whowechina/chord_pico/ref/GJqL9p1aUAAI2bQ.jpg

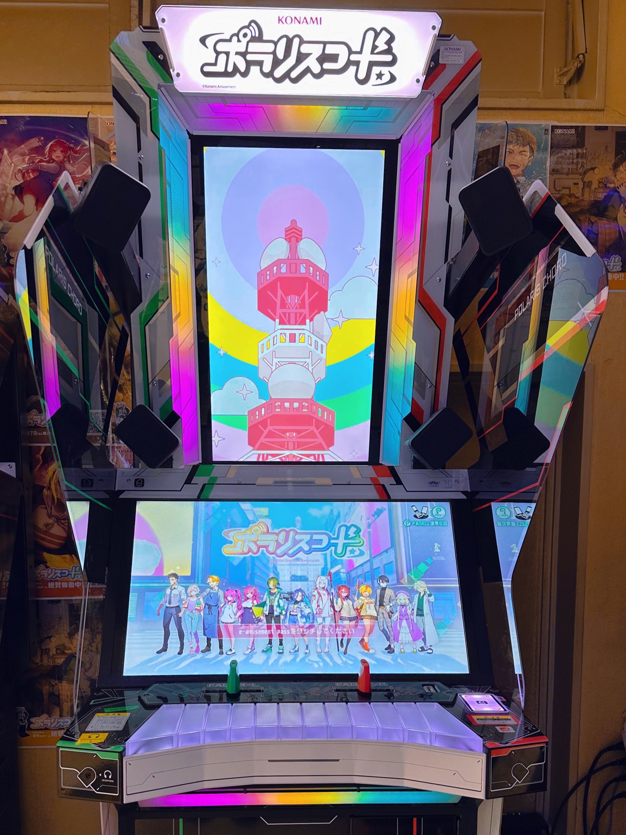
ref/GJqL9p1aUAAI2bQ.jpg
