whowechina/chord_pico/ref/Knob.png

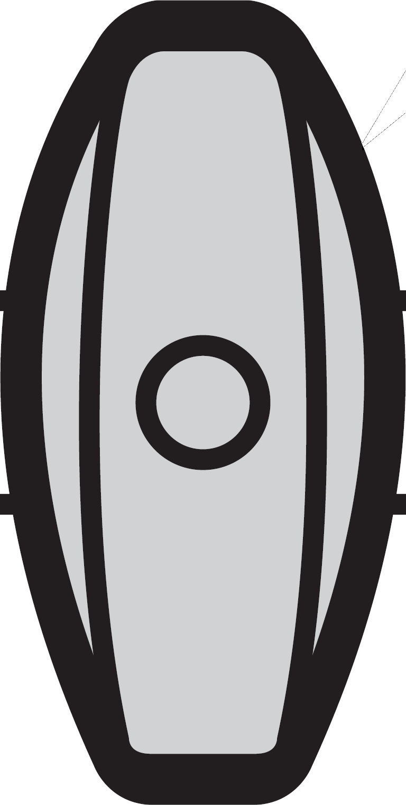
ref/Knob.png
