whowechina/chord_pico/ref/Panel2.png

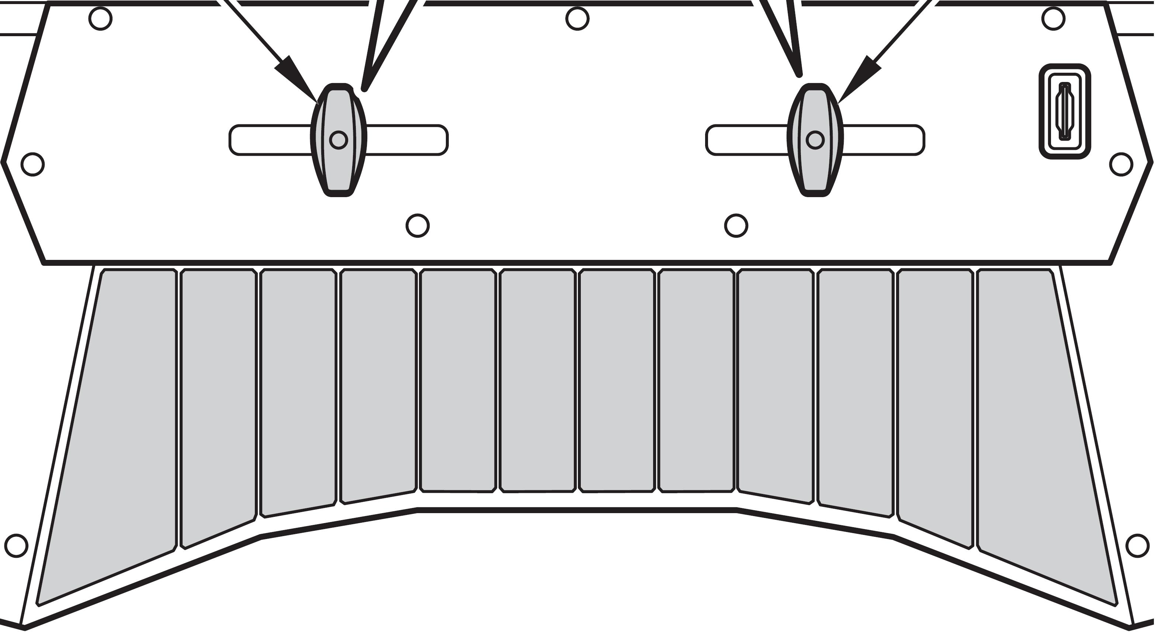
ref/Panel2.png
