whowechina/chord_pico/ref/Panel.png

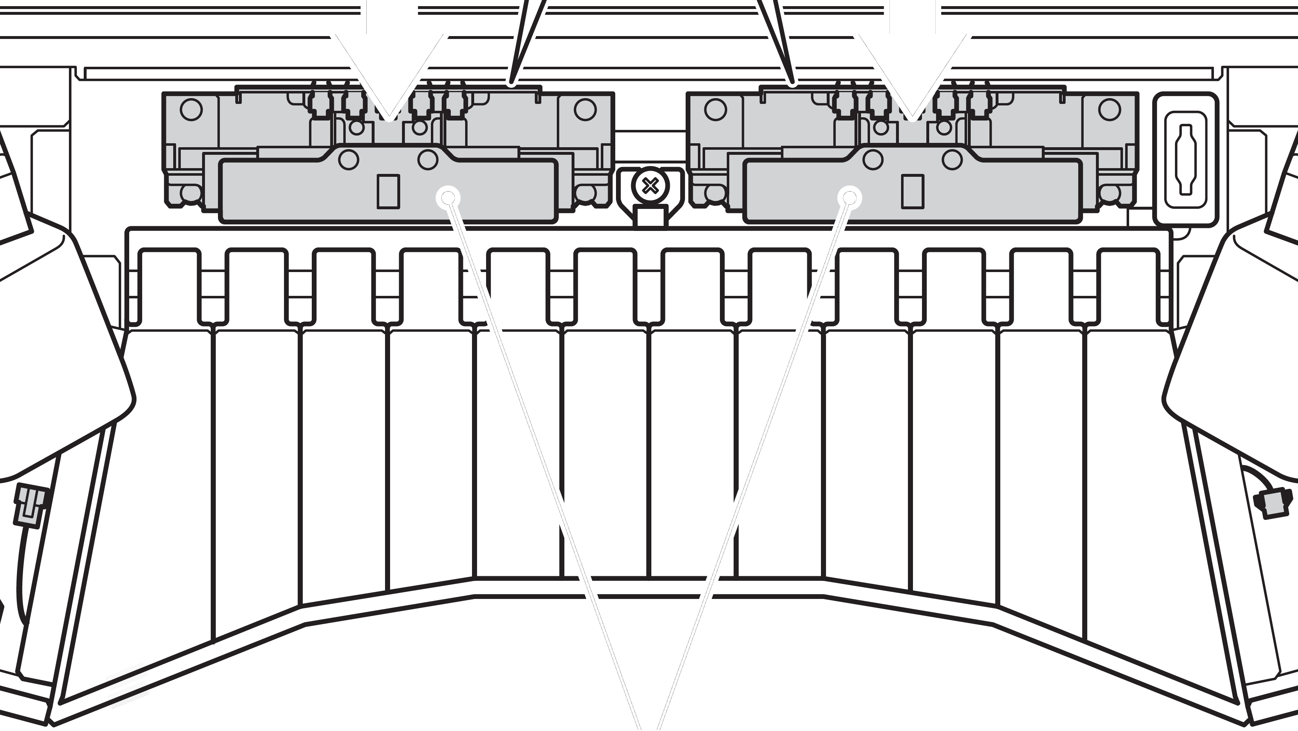
ref/Panel.png
