whowechina/chord_pico/Production/3DPrint/Chord Pico+ - BrimLeft.stl

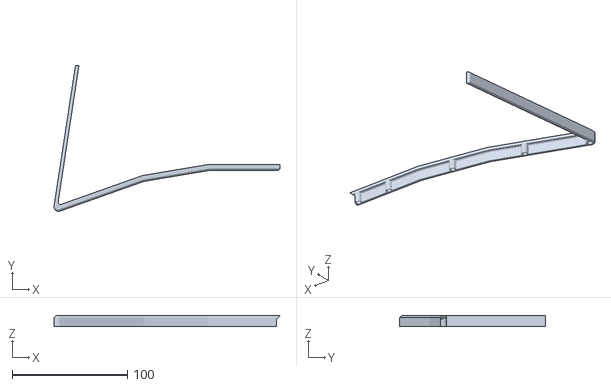
[picture p42: CAD file, 2026-01-07]
Production/3DPrint/Chord Pico+ - BrimLeft.stl
196.0 x 126.4 x 9.20
