whowechina/chord_pico/PCB/plus/3dmodels/TRS Jack PJ-313.stp

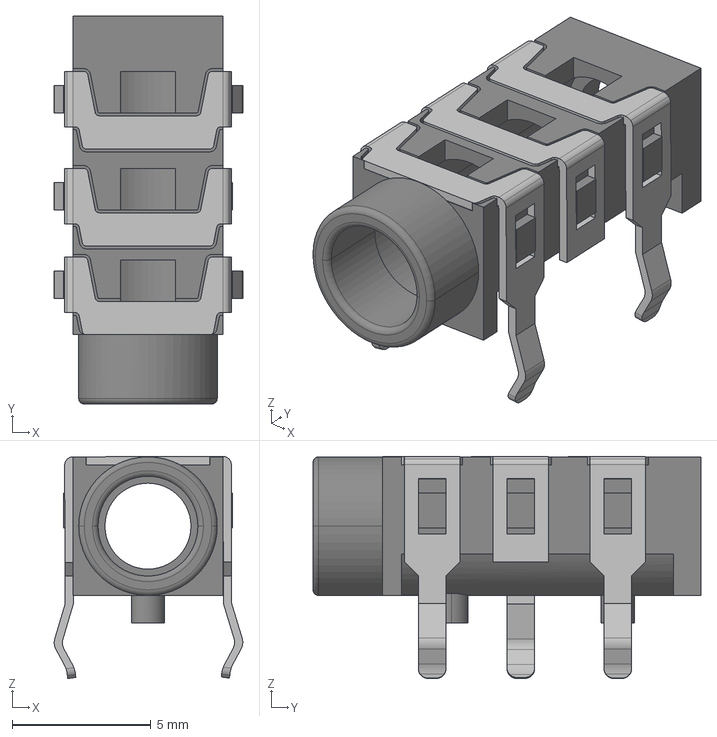
[picture p43: CAD file, 2025-06-20]
PCB/plus/3dmodels/TRS Jack PJ-313.stp
6.81 x 14.0 x 8.02 mm
