whowechina/chord_pico/Production/3DPrint/Chord Pico+ - BrimRight.stl

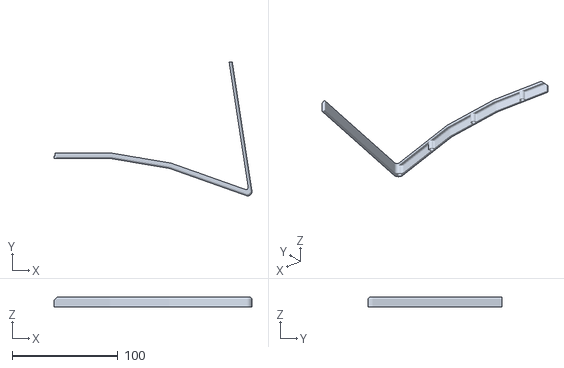
[picture p44: CAD file, 2026-01-07]
Production/3DPrint/Chord Pico+ - BrimRight.stl
187.0 x 126.4 x 9.20
