whowechina/chord_pico/PCB/plus/3dmodels/SW_Kailh_Choc_V1.stp

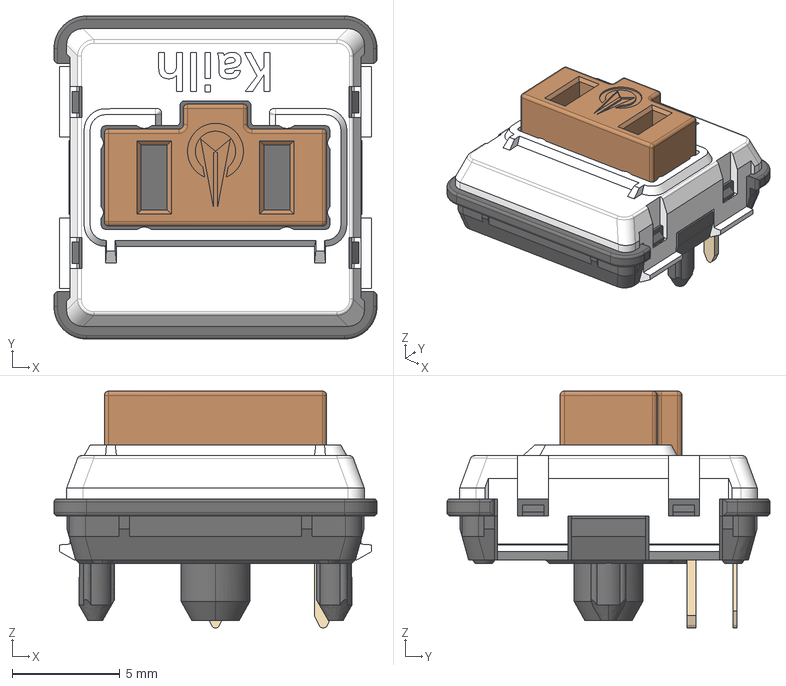
[picture p45: CAD file, 2025-06-20]
PCB/plus/3dmodels/SW_Kailh_Choc_V1.stp
15.0 x 15.0 x 11.0 mm
