whowechina/chord_pico/Production/3DPrint/Fader+ - Reflector.stl

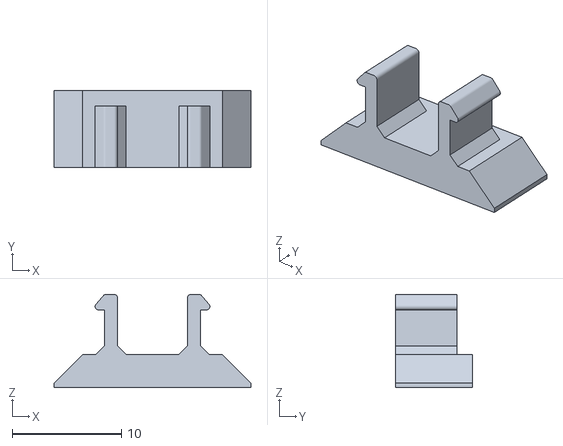
[picture p46: CAD file, 2026-01-07]
Production/3DPrint/Fader+ - Reflector.stl
18.0 x 7.00 x 8.50
