whowechina/chord_pico/Production/3DPrint/Chord Pico+ - Right.stl

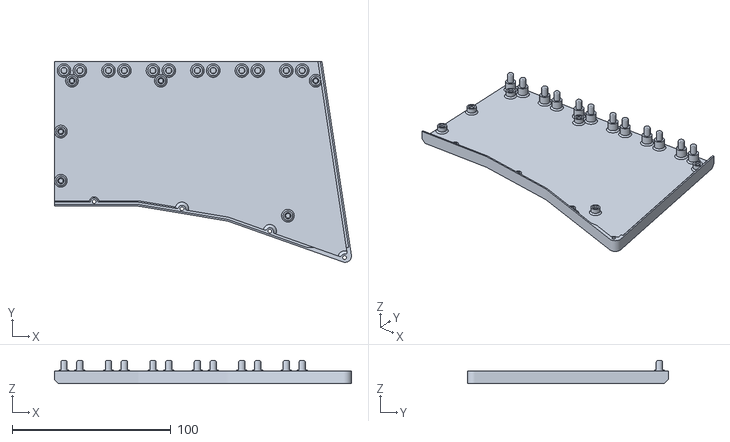
[picture p48: CAD file, 2026-01-07]
Production/3DPrint/Chord Pico+ - Right.stl
187.0 x 126.4 x 14.5
