whowechina/chord_pico/PCB/plus/3dmodels/SPEAKER_SMD_1340.STEP

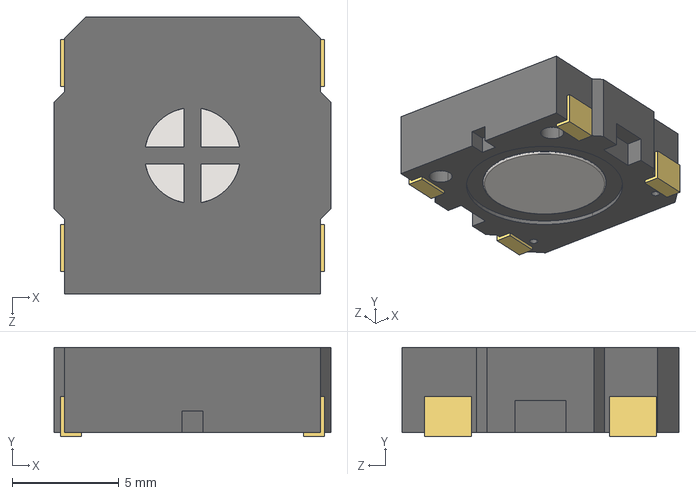
[picture p49: CAD file, 2025-06-20]
PCB/plus/3dmodels/SPEAKER_SMD_1340.STEP
13.0 x 4.20 x 13.0 mm
