whowechina/chord_pico/Production/3DPrint/Fader+ - Seat+.stl

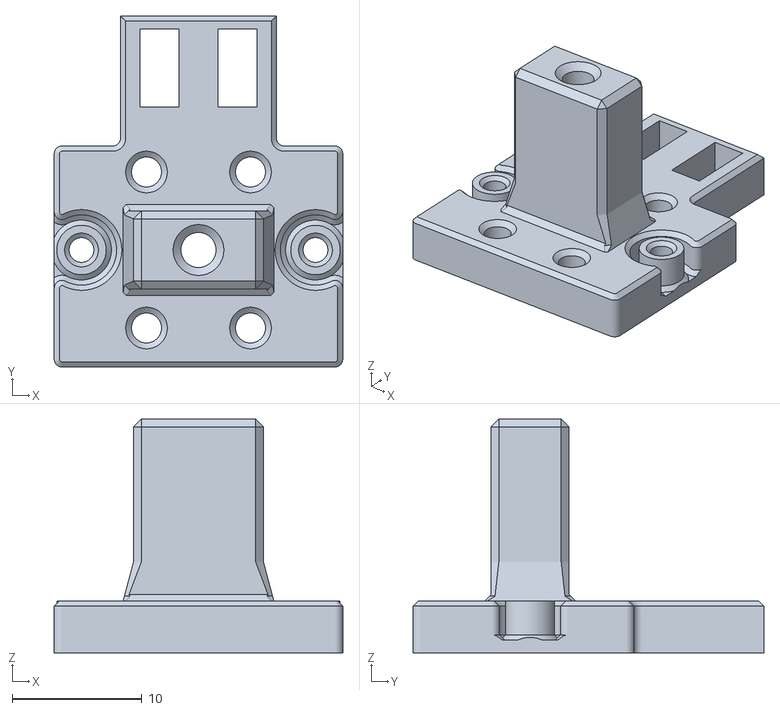
[picture p50: CAD file, 2026-01-07]
Production/3DPrint/Fader+ - Seat+.stl
22.2 x 27.0 x 18.0
