whowechina/chord_pico/PCB/plus/3dmodels/8002A.step

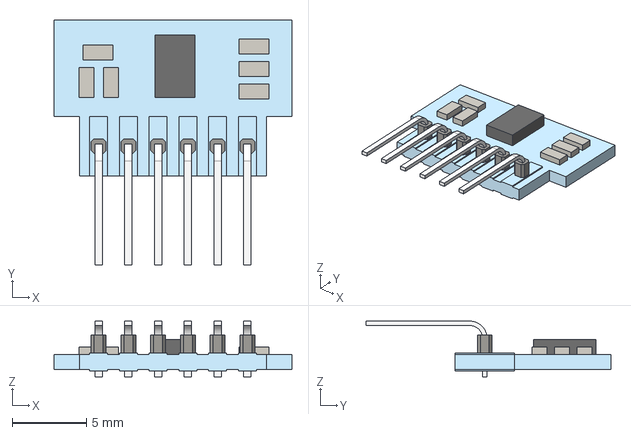
[picture p51: CAD file, 2025-06-20]
PCB/plus/3dmodels/8002A.step
16.0 x 16.5 x 3.75 mm
