whowechina/chord_pico/Production/3DPrint/Chord Pico+ - Left.stl

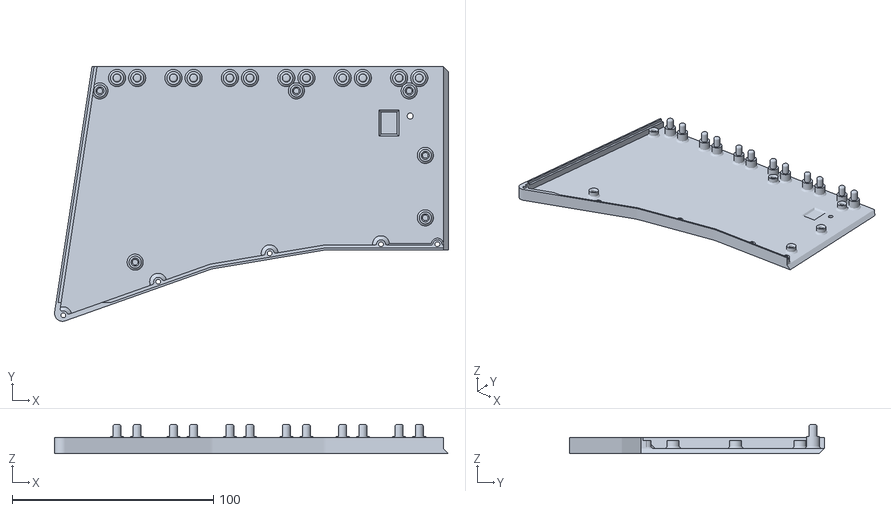
[picture p52: CAD file, 2026-01-07]
Production/3DPrint/Chord Pico+ - Left.stl
195.5 x 126.4 x 14.5
