whowechina/chord_pico/PCB/plus/3dmodels/WS2812B.step

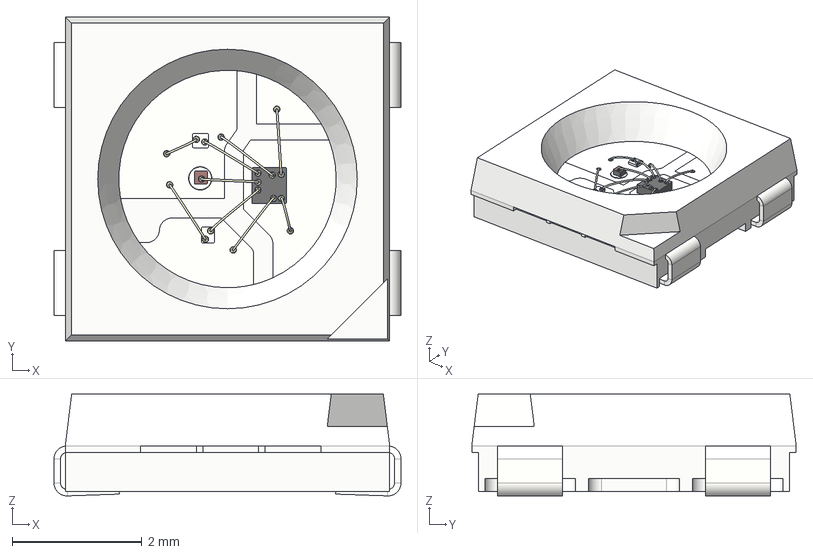
[picture p53: CAD file, 2025-06-20]
PCB/plus/3dmodels/WS2812B.step
5.35 x 5.00 x 1.57 mm
