whowechina/chord_pico/Production/3DPrint/Chord Pico+ - Rear.stl

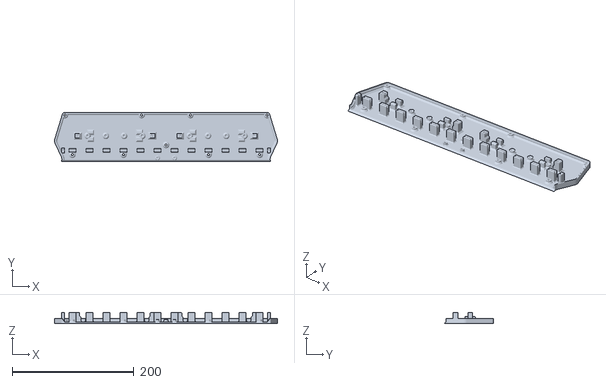
[picture p54: CAD file, 2026-01-07]
Production/3DPrint/Chord Pico+ - Rear.stl
366.7 x 81.1 x 18.2
