whowechina/chord_pico/Production/3DPrint/Fader - Slider PTFE.stl

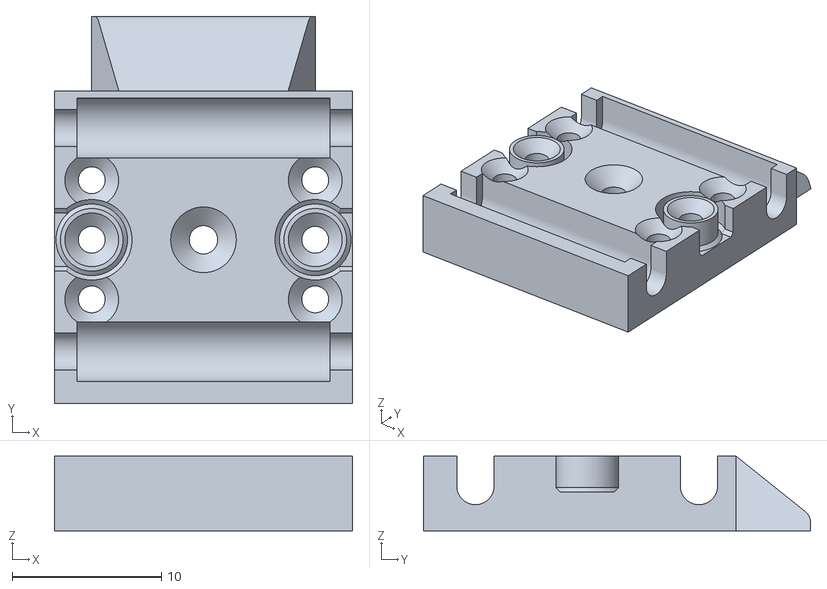
[picture p56: CAD file, 2025-09-20]
Production/3DPrint/Fader - Slider PTFE.stl
20.0 x 26.0 x 5.00
