whowechina/chord_pico/PCB/plus/3dmodels/skhhana010.stp

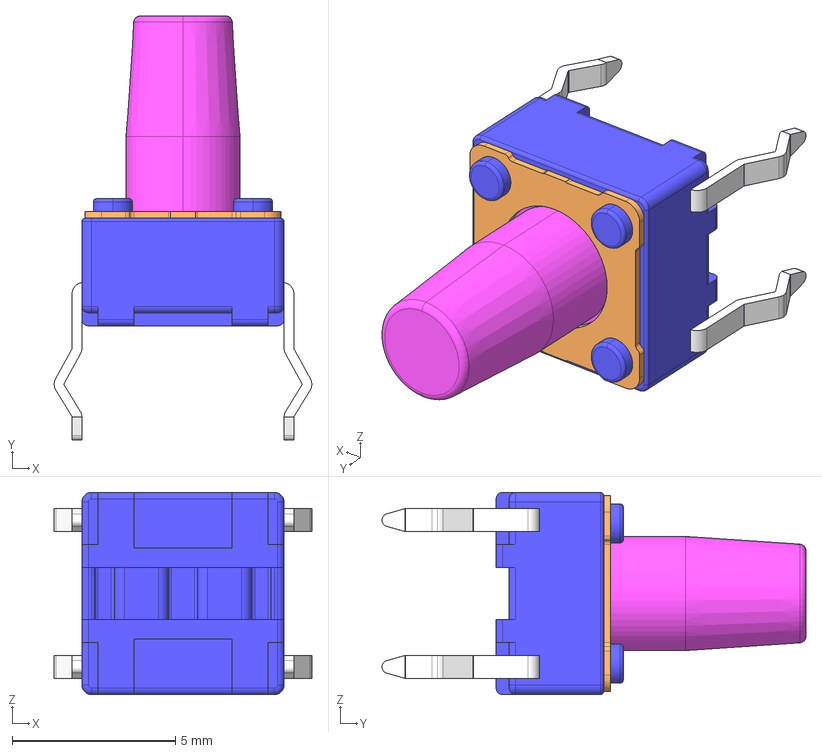
[picture p57: CAD file, 2025-06-20]
PCB/plus/3dmodels/skhhana010.stp
7.90 x 13.0 x 6.20 mm
