whowechina/chord_pico/Production/3DPrint/Fader - Slider Thruhole.stl

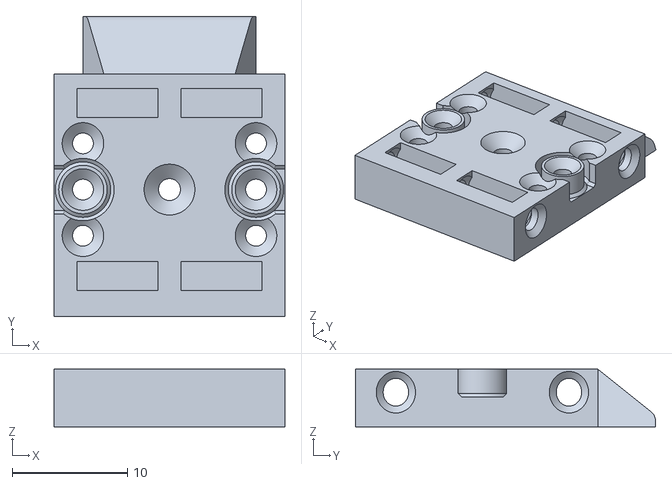
[picture p58: CAD file, 2025-09-20]
Production/3DPrint/Fader - Slider Thruhole.stl
20.0 x 26.0 x 5.00
