whowechina/chord_pico/PCB/plus/3dmodels/SKRRABE010.stp

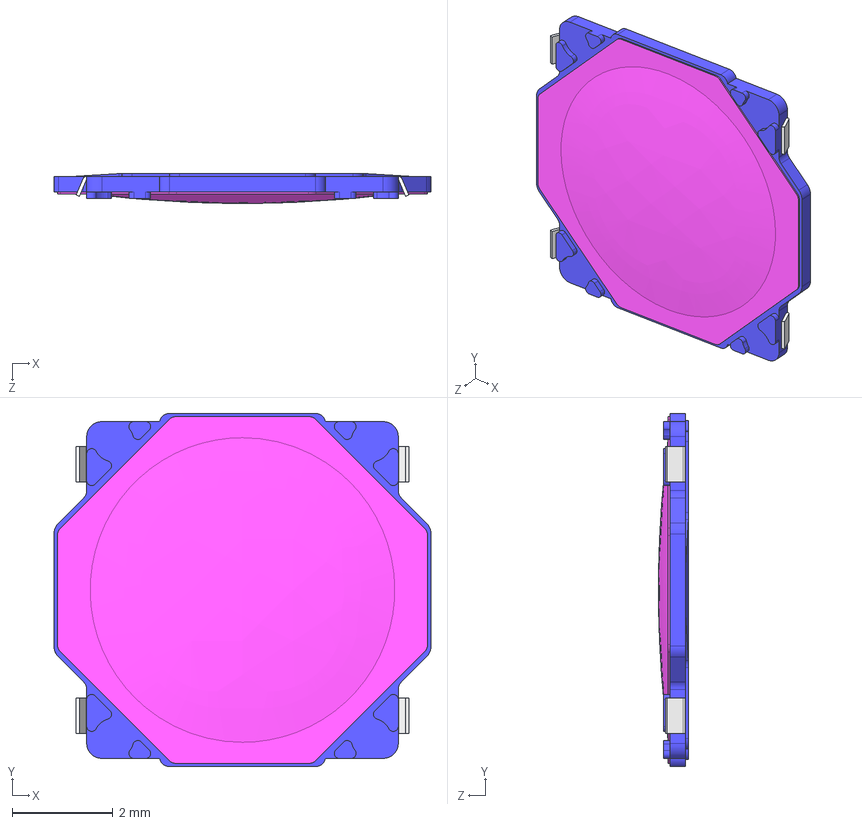
[picture p59: CAD file, 2025-06-20]
PCB/plus/3dmodels/SKRRABE010.stp
7.50 x 7.03 x 0.6 mm
