whowechina/chord_pico/Production/3DPrint/Fader - Slider Seal.stl

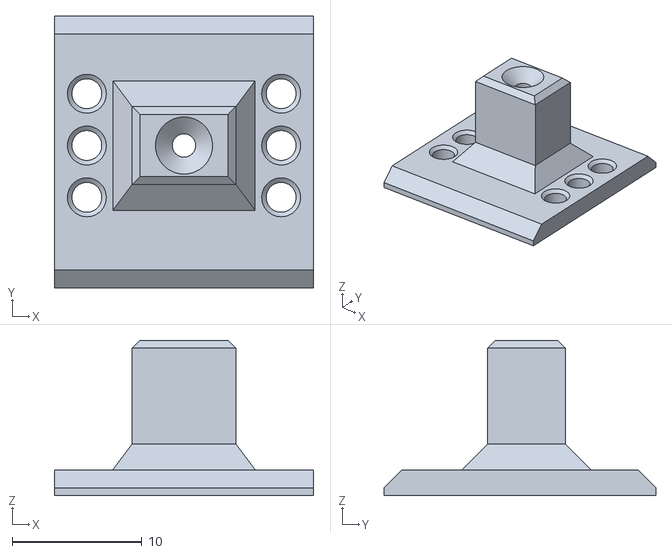
[picture p60: CAD file, 2025-09-20]
Production/3DPrint/Fader - Slider Seal.stl
20.0 x 21.0 x 12.0
