whowechina/chord_pico/PCB/plus/3dmodels/SW-DTSA-63K-V.stp

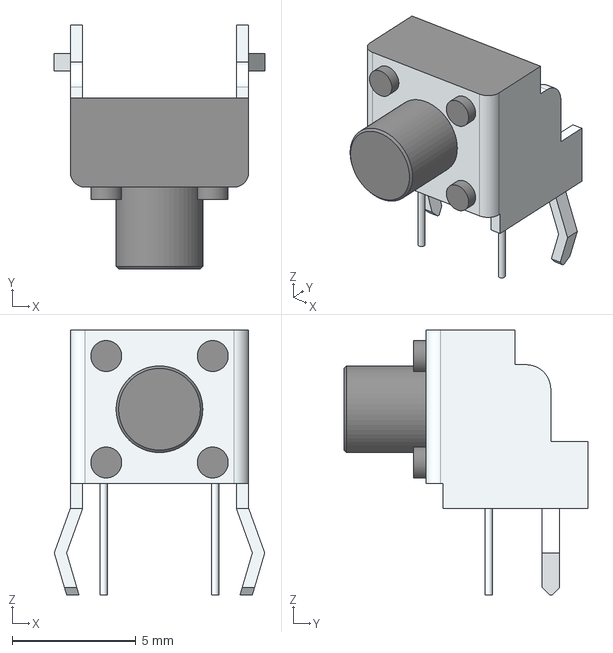
[picture p61: CAD file, 2025-06-20]
PCB/plus/3dmodels/SW-DTSA-63K-V.stp
8.50 x 9.85 x 10.7 mm
