whowechina/chord_pico/Production/3DPrint/Chord Pico - Brim.stl

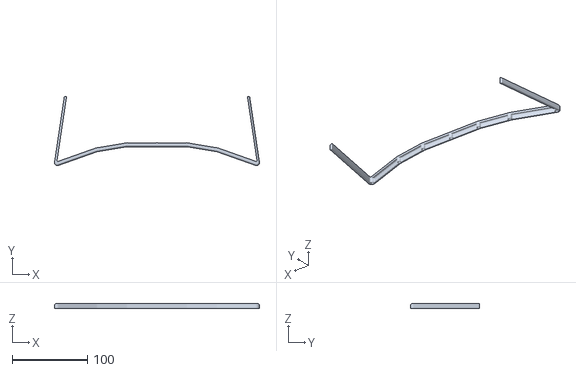
[picture p62: CAD file, 2025-09-20]
Production/3DPrint/Chord Pico - Brim.stl
273.1 x 92.1 x 7.00
