whowechina/chord_pico/PCB/plus/3dmodels/dcdc_3to5.step

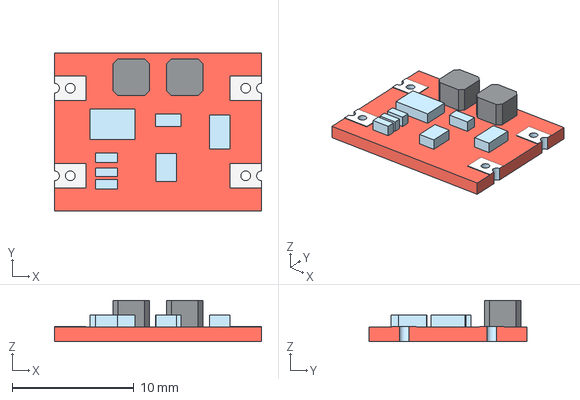
[picture p63: CAD file, 2025-06-20]
PCB/plus/3dmodels/dcdc_3to5.step
17.0 x 13.0 x 3.40 mm
