whowechina/chord_pico/PCB/plus/3dmodels/WS2812-2020.STEP

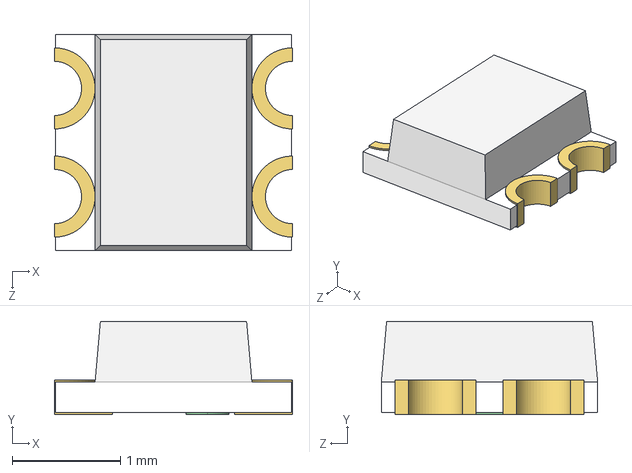
[picture p64: CAD file, 2025-06-20]
PCB/plus/3dmodels/WS2812-2020.STEP
2.20 x 0.86 x 2.00 mm
