whowechina/chord_pico/Production/3DPrint/Chord Pico - Rail Fixer.stl

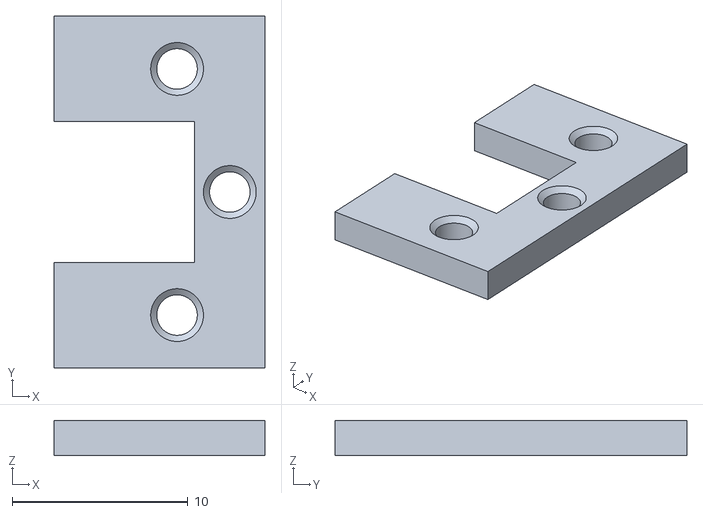
[picture p65: CAD file, 2025-09-20]
Production/3DPrint/Chord Pico - Rail Fixer.stl
12.0 x 20.0 x 2.00
