whowechina/chord_pico/PCB/plus/3dmodels/J 2835.step

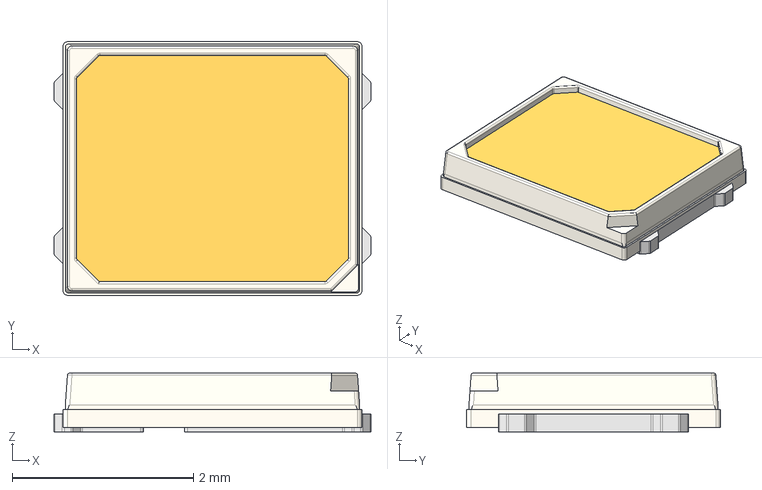
[picture p66: CAD file, 2025-06-20]
PCB/plus/3dmodels/J 2835.step
3.50 x 2.80 x 0.65 mm
