whowechina/chord_pico/PCB/plus/3dmodels/WS2812-0807.STEP

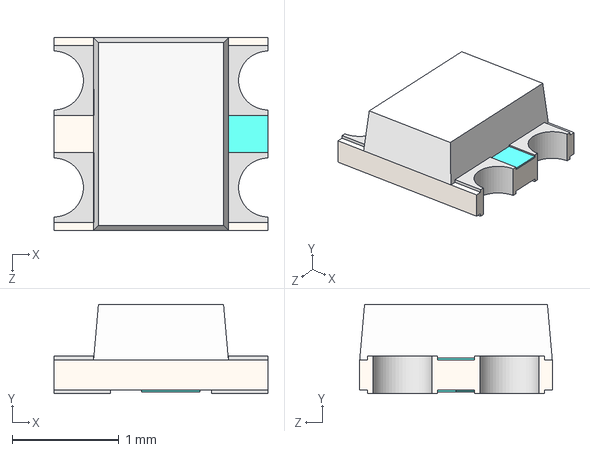
[picture p67: CAD file, 2025-06-20]
PCB/plus/3dmodels/WS2812-0807.STEP
2.00 x 0.835 x 1.80 mm
