whowechina/chord_pico/PCB/plus/3dmodels/skhhbva010.stp

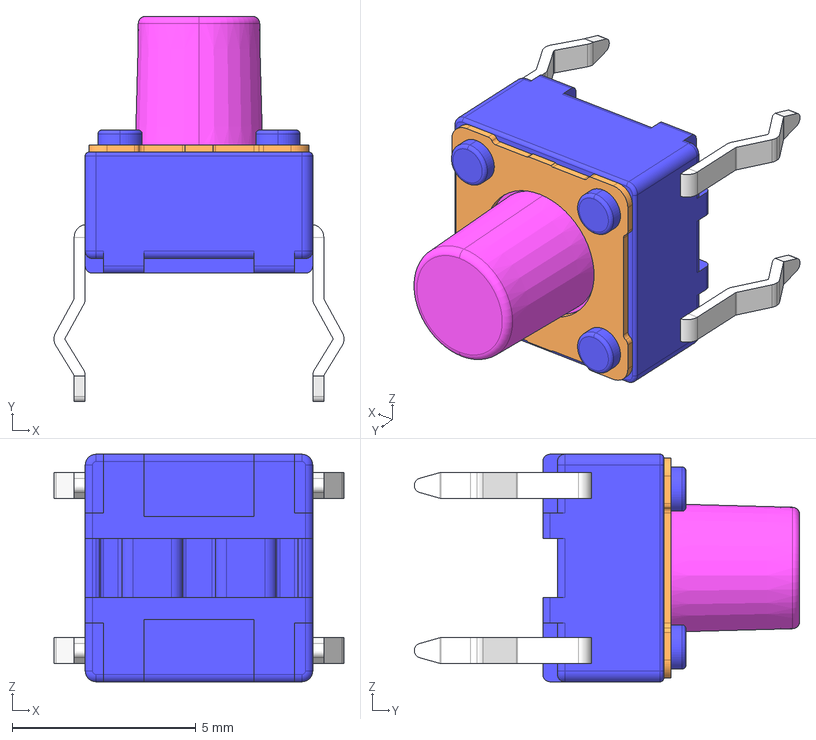
[picture p68: CAD file, 2025-06-20]
PCB/plus/3dmodels/skhhbva010.stp
7.90 x 10.5 x 6.20 mm
