whowechina/chord_pico/PCB/plus/3dmodels/SKPMAM.STEP

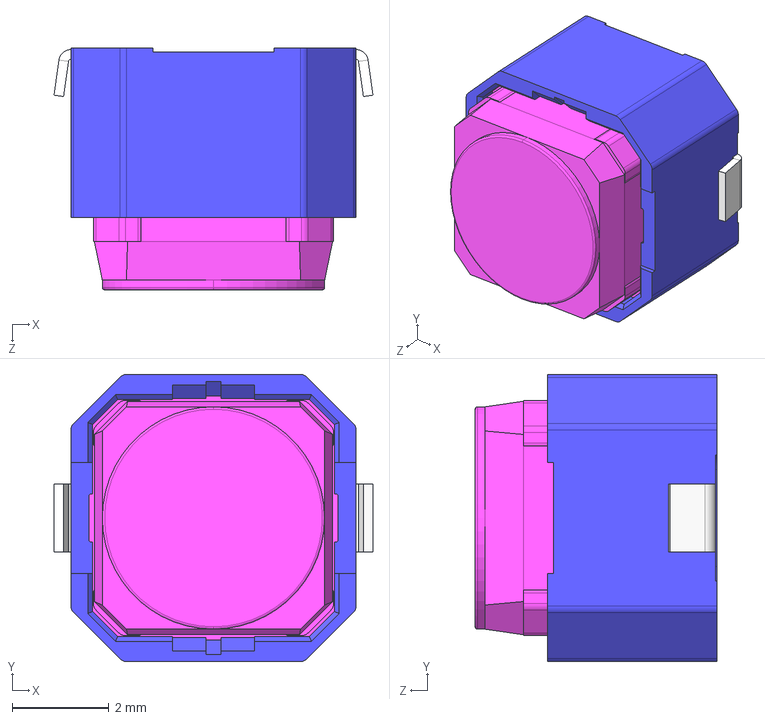
[picture p70: CAD file, 2025-06-20]
PCB/plus/3dmodels/SKPMAM.STEP
6.60 x 5.94 x 5.00 mm
