whowechina/chord_pico/PCB/plus/3dmodels/Tact Switch 4.5mm SMT.step

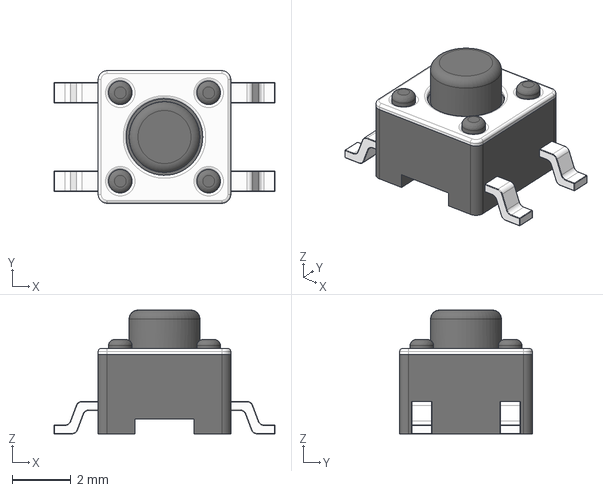
[picture p71: CAD file, 2025-06-20]
PCB/plus/3dmodels/Tact Switch 4.5mm SMT.step
7.50 x 4.50 x 4.20 mm
