whowechina/chord_pico/PCB/plus/3dmodels/SS49E.step

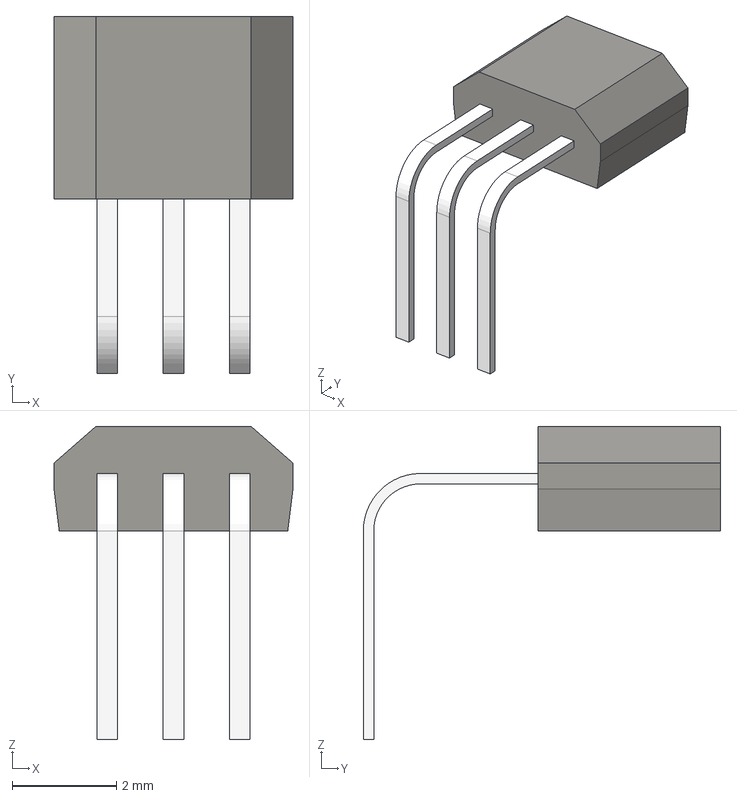
[picture p72: CAD file, 2025-06-20]
PCB/plus/3dmodels/SS49E.step
4.58 x 6.85 x 6.00 mm
