whowechina/chord_pico/PCB/plus/3dmodels/User Library-WS2812-2020.step

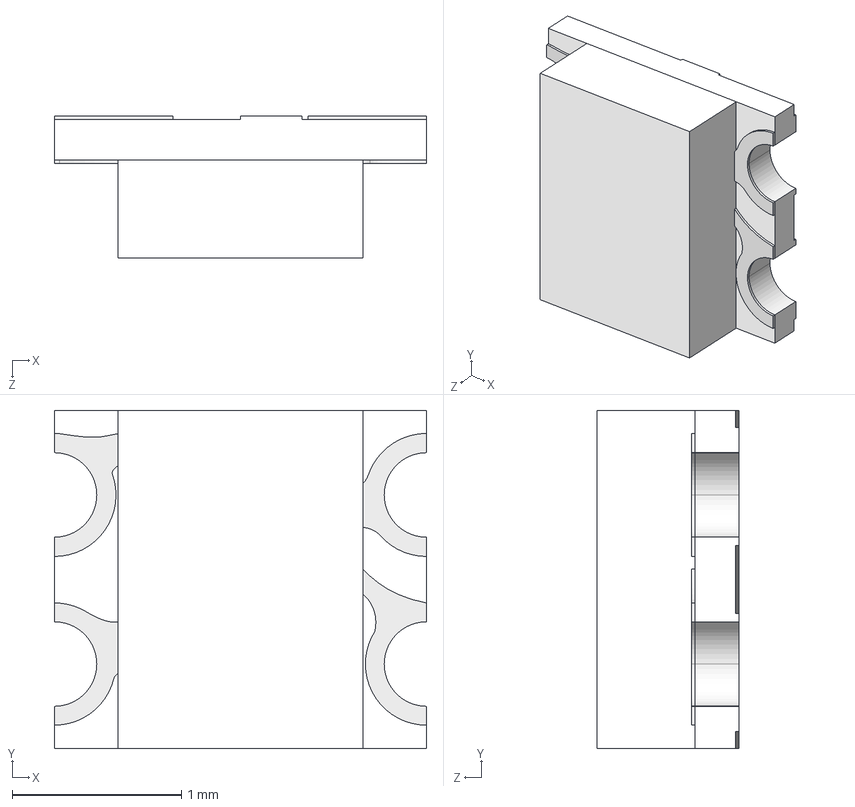
[picture p73: CAD file, 2025-06-20]
PCB/plus/3dmodels/User Library-WS2812-2020.step
2.20 x 2.00 x 0.84 mm
