whowechina/chord_pico/PCB/plus/3dmodels/Button Cap.step

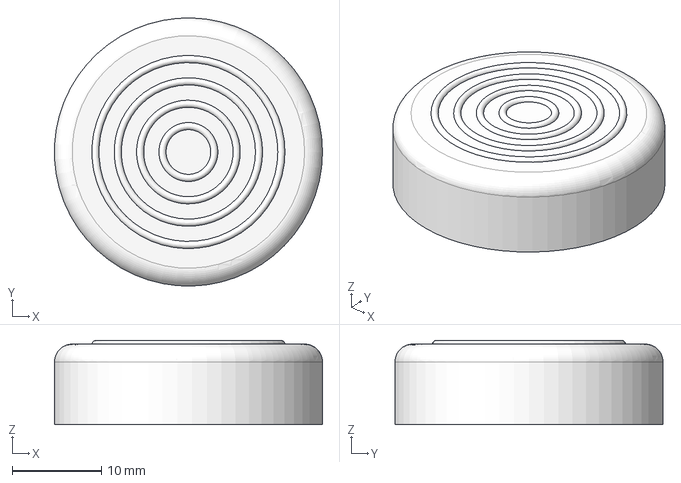
[picture p74: CAD file, 2025-06-20]
PCB/plus/3dmodels/Button Cap.step
30.0 x 30.0 x 9.40 mm
