whowechina/chord_pico/PCB/plus/3dmodels/EVQ-P1D05M.stp

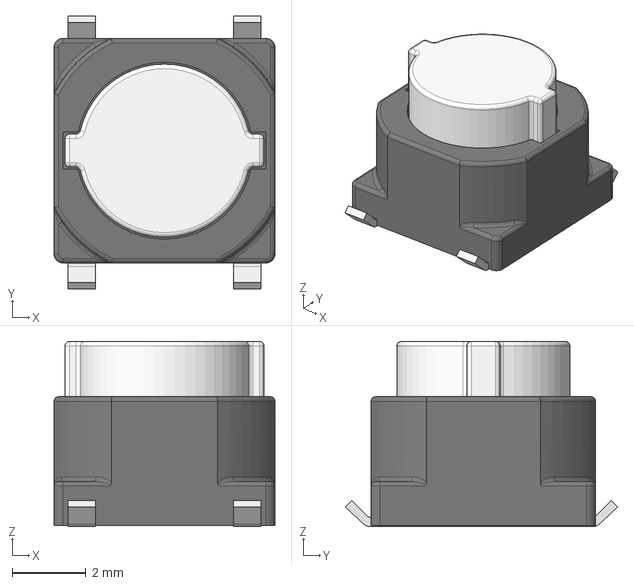
[picture p75: CAD file, 2025-06-20]
PCB/plus/3dmodels/EVQ-P1D05M.stp
6.00 x 7.40 x 5.03 mm
