whowechina/chord_pico/PCB/plus/3dmodels/SMD WS2812B-3535.step

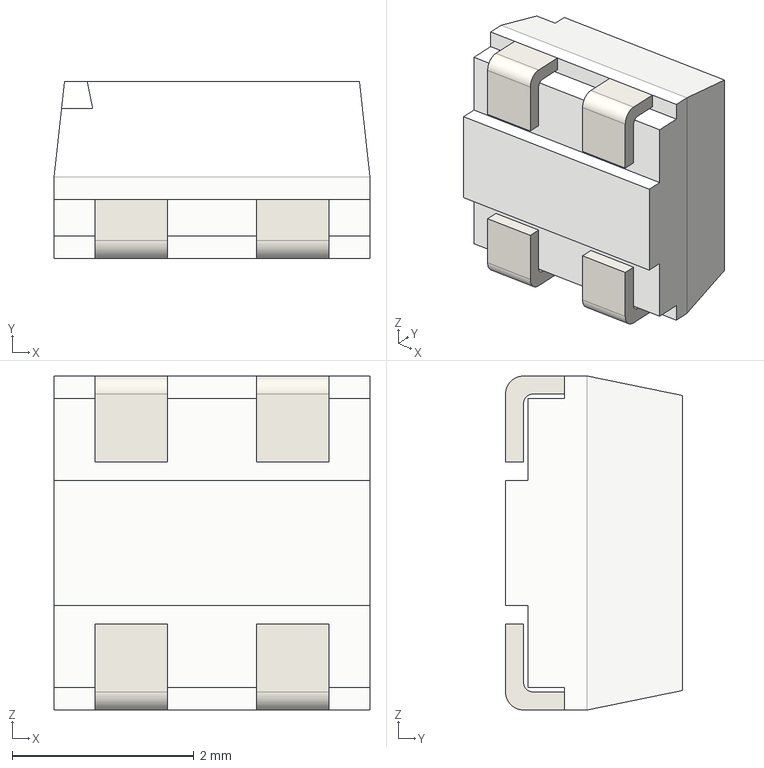
[picture p76: CAD file, 2025-06-20]
PCB/plus/3dmodels/SMD WS2812B-3535.step
3.48 x 1.95 x 3.68 mm
