whowechina/chord_pico/PCB/plus/3dmodels/SKSTAAE010.stp

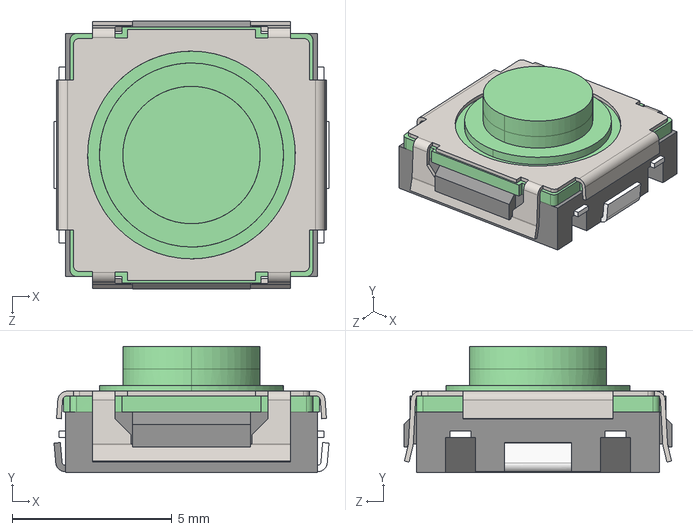
[picture p77: CAD file, 2025-06-20]
PCB/plus/3dmodels/SKSTAAE010.stp
8.61 x 3.95 x 8.40 mm
