whowechina/chord_pico/PCB/plus/3dmodels/Kailh_PG1353.STEP

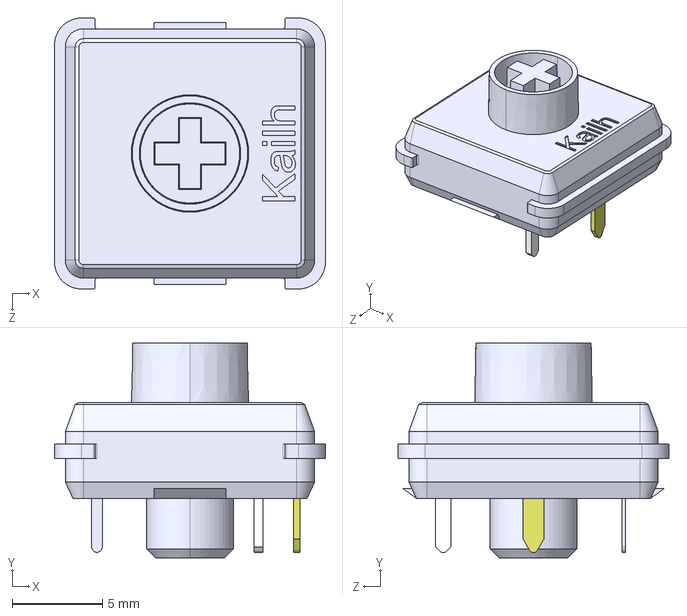
[picture p79: CAD file, 2025-06-20]
PCB/plus/3dmodels/Kailh_PG1353.STEP
15.0 x 11.9 x 15.0 mm
