whowechina/chord_pico/PCB/plus/3dmodels/FPC0.5MM1.0H18P.step

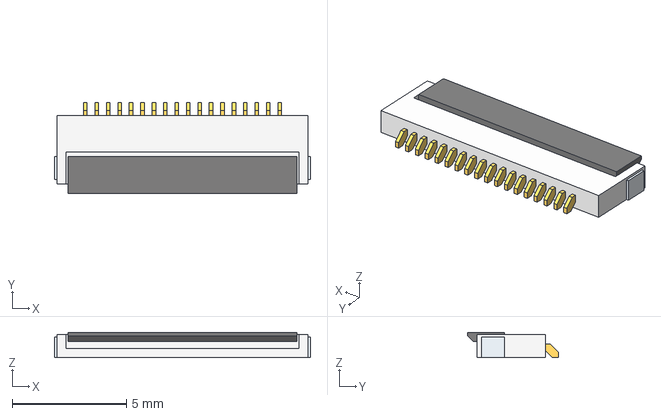
[picture p80: CAD file, 2025-06-20]
PCB/plus/3dmodels/FPC0.5MM1.0H18P.step
11.2 x 3.96 x 1.10 mm
