whowechina/chord_pico/firmware/src/commands.c

#include <stdio.h>
#include <stdlib.h>
#include <string.h>
#include <fcntl.h>
#include <ctype.h>

#include "pico/stdio.h"
#include "pico/stdlib.h"

#include "config.h"
#include "save.h"
#include "cli.h"

#include "hall.h"

#include "usb_descriptors.h"

#define SENSE_LIMIT_MAX 9
#define SENSE_LIMIT_MIN -9

static void disp_light()
{
    printf("[Light]\n");
    printf("  Key Level: %d.\n", chord_cfg->light.level_key);
    printf("  Fader Level: %d.\n", chord_cfg->light.level_fader);
}

static void disp_hall()
{
    printf("[Hall Effect Button]\n");
    for (int i = 0; i < hall_keynum(); i++) {
        if (!hall_is_present(i)) {
            printf("  Key %2d: Not Present.\n", i + 1);
            continue;
        }
        printf("  Key %2d: %4d->%4d, On: %2d, Off: %2d.\n",
               i + 1, chord_cfg->calibrated.up[i], chord_cfg->calibrated.down[i],
                chord_cfg->trigger.on[i] + 1, chord_cfg->trigger.off[i] + 1);
    }
}

static void disp_hid()
{
    printf("[HID]\n");
    printf("  Report Fader Raw: %s.\n", chord_cfg->hid.raw_fader ? "On" : "Off");
}

void handle_display(int argc, char *argv[])
{
    const char *usage = "Usage: display [light|hall|hid]\n";
    if (argc > 1) {
        printf(usage);
        return;
    }

    if (argc == 0) {
        disp_light();
        disp_hall();
        disp_hid();
        return;
    }

    const char *choices[] = {"light", "hall", "hid"};
    switch (cli_match_prefix(choices, count_of(choices), argv[0])) {
        case 0:
            disp_light();
            break;
        case 1:
            disp_hall();
            break;
        case 2:
            disp_hid();
        default:
            printf(usage);
            break;
    }
}

static void handle_level(int argc, char *argv[])
{
    const char *usage = "Usage: level <key|fader> <0..255>\n";
    if (argc != 2) {
        printf(usage);
        return;
    }

    const char *choices[] = {"key", "fader"};
    int match = cli_match_prefix(choices, count_of(choices), argv[0]);
    if (match < 0) {
        printf(usage);
        return;
    }

    int level = cli_extract_non_neg_int(argv[1], 0);
    if ((level < 0) || (level > 255)) {
        printf(usage);
        return;
    }

    if (match == 0) {
        chord_cfg->light.level_key = level;
    } else if (match == 1) {
        chord_cfg->light.level_fader = level;
    }
    config_changed();
    disp_light();
}

static void handle_calibrate(int argc, char *argv[])
{
    hall_calibrate();
}

static void handle_trigger(int argc, char *argv[])
{
    const char *usage = "Usage: trigger <all|KEY> <ON> <OFF>\n"
                        "  KEY: 1..%d\n"
                        "   ON: 1..36, distance for actuation.\n"
                        "  OFF: 1..36, distance for reset.\n";
    if (argc != 3) {
        printf(usage, hall_keynum());
        return;
    }

    bool all_key = (strncasecmp(argv[0], "all", strlen(argv[0])) == 0);
    int key = cli_extract_non_neg_int(argv[0], 0) - 1;
    int on = cli_extract_non_neg_int(argv[1], 0) - 1;
    int off = cli_extract_non_neg_int(argv[2], 0) - 1;
    
    if ((!all_key && (key < 0)) || (key >= hall_keynum()) ||
        (on < 0) || (on > 35) || (off < 0) || (off > 35)) {
        printf(usage, hall_keynum());
        return;
    }

    for (int i = 0; i < hall_keynum(); i++) {
        if (all_key || (i == key)) {
            chord_cfg->trigger.on[i] = on;
            chord_cfg->trigger.off[i] = off;
        }
    }
    config_changed();

    disp_hall();
}

static void handle_raw_fader(int argc, char *argv[])
{
    const char *usage = "Usage: raw_fader <on|off>\n";

    if (argc != 1) {
        printf(usage);
        return;
    }

    const char *choices[] = {"on", "off"};
    int match = cli_match_prefix(choices, count_of(choices), argv[0]);
    if (match < 0) {
        printf(usage);
        return;
    }

    chord_cfg->hid.raw_fader = (match == 0);
    config_changed();
    disp_hid();
}

static void handle_debug(int argc, char *argv[])
{
    const char *usage = "Usage: debug <hall|fader>\n";
    if (argc != 1) {
        printf(usage);
        return;
    }
    const char *choices[] = {"hall", "fader"};
    switch (cli_match_prefix(choices, count_of(choices), argv[0])) {
        case 0:
            chord_runtime.debug.hall ^= true;
            break;
        case 1:
            chord_runtime.debug.fader ^= true;
            break;
        default:
            printf(usage);
            break;
    }
}

static void handle_save()
{
    save_request(true);
}

static void handle_factory_reset()
{
    config_factory_reset();
    printf("Factory reset done.\n");
}

void commands_init()
{
    cli_register("display", handle_display, "Display all config.");
    cli_register("level", handle_level, "Set LED brightness level.");
    cli_register("calibrate", handle_calibrate, "Calibrate the key sensors.");
    cli_register("trigger", handle_trigger, "Set Hall effect switch triggering.");
    cli_register("raw_fader", handle_raw_fader, "Set if raw fader is included in HID report.");
    cli_register("debug", handle_debug, "Toggle debug features.");
    cli_register("save", handle_save, "Save config to flash.");
    cli_register("factory", handle_factory_reset, "Reset everything to default.");
}
